supermoun62/Projet_Telerupteur_RF433_V2/Liste_Materiel_Emetteur_Recepteur_Telerupteur_RF433_V2/Liste_Materiel_Emetteur_Telerupteur_RF433_V2.pdf

Liste_Materiel_Emetteur_Telerupteur_RF433_V2

Page 1 sur 1 | https://electroniquepassion.fr/
Reference | Value | TME Electronic | SeedStudio | GoTronic | Lextronic | Conrad
U3 | A000005
J2 | PinHeader_1x02_P2.54mm
D4 | R 2v | SLR-56VR3F (https://www.tme.eu/fr/katalog/?art=SLR-56VR3F)
R2, R4 | 10k - 1 % | MRS25000C1002FCT00 (https://www.tme.eu/fr/katalog/?art=MRS25000C1002FCT00)
J4 | PinHeader_1x03_P2.54mm
U4 | Emetteur | | 113990010 | 05294 (https://www.gotronic.fr/art-kit-emetteur-recepteur-433mhz-18881.htm)
U2 | 24LC256-I_P
R6, R7 | 4k7 - 1 % | MBB02070C4701FCT00 (https://www.tme.eu/fr/katalog/?art=MBB02070C4701FCT00)
J3 | PinHeader_1x01_P2.54mm
D3 | R 2v | SLR-56VR3F (https://www.tme.eu/fr/katalog/?art=SLR-56VR3F)
R8 | 1K5 - 1 % | MRS25000C1501FCT00 (https://www.tme.eu/fr/details/mrs25000c1501fct00/resistances-metallisees-tht-0-6w/vishay/)
D5 | R 2v | SLR-56VR3F (https://www.tme.eu/fr/katalog/?art=SLR-56VR3F)
F1 | 100mA
Support Fusible | | | | | | 530127 (https://www.conrad.fr/p/porte-fusible-eska-506000-506000-adapte-pour-fusible-5-x-20-mm-63-a-250-vac-1-pcs-530127)
D2 | V 2v | OSNG5134A (https://www.tme.eu/fr/details/osng5134a/diodes-led-tht-5mm/optosupply/)
R1, R3, R5 | 3K9 - 1 % | MBB02070C3901FC100 (https://www.tme.eu/fr/details/mbb02070c3901fc100/resistances-metallisees-tht-0-6w/vishay/)
U1 | L7809 | NTE1910 (https://www.tme.eu/fr/details/nte1910/stabilisateurs-de-tension-non-regles/nte-electronics/)
Refroidisseur | | FK210SACB (https://www.tme.eu/fr/details/fk210sacb/radiateurs/fischer-elektronik/)
| Pâte thermique KP12 4.2 g 10 W/mK | | | | | 189069 (https://www.conrad.fr/p/pate-thermique-kerafol-kp12-42-g-10-wmk-temperature-max-150-c-42-g-189069)
C3 | 100nf | CCK-100N (https://www.tme.eu/fr/details/cck-100n/condensateurs-ceramiques-tht-100v/sr-passives/)
C2 | 330nf | BFC233820334 (https://www.tme.eu/fr/details/bfc233820334/condensateurs-polypropylene-x2-y2/vishay/)
C1 | 2200uf | KM2200/25 (https://www.tme.eu/fr/details/km2200_25/condensateurs-electrolytiques-tht-105degc/samxon/km-2200u-25v/)
TR1 | BVEI3022938 220v -12v -1,2VA | BVEI3022938 (https://www.tme.eu/fr/katalog/?search=BVEI3032012&s_field=1000011&s_order=desc)
D1 | B40C1500G | B40C1500G-E4/51 (https://www.tme.eu/fr/details/b40c1500g-e4_51/redresseurs-monophases-a-diodes-ronds/vishay/)
J1 | Conn_01x03 | MKDS 1,5/ 3-5,08 1715734 | | | | 743464 (https://www.conrad.fr/p/bornier-a-vis-phoenix-contact-mkds-15-3-508-1715734-150-mm-nombre-de-poles-3-vert-1-pcs-743464)

Support 8b

Fil pour Arduino | 25932 (https://www.gotronic.fr/art-pack-de-cables-de-connexion-12411.htm)
Strap | | 15-AT (https://www.lextronic.fr/cavalier-pas-2-54-mm-3613.html)
Con Header mâle | 48004 (https://www.gotronic.fr/art-connecteur-ard010-18114.htm) | CC076 (https://www.lextronic.fr/module/ambjolisearch/jolisearch?s=cc076)
