supermoun62/Projet_Telerupteur_RF433_V2/Liste_Materiel_Emetteur_Recepteur_Telerupteur_RF433_V2/Liste_Materiel_Recepteur_Telerupteur_RF433_V2.pdf

Liste_Materiel_Recepteur_Telerupteur_RF433_V2

Page 1 sur 1 | https://electroniquepassion.fr/
Reference | Value | TME Electronic | SeedStudio | GoTronic | Lextronic | Farnell
C1 | 2200uf | KM2200/25 (https://www.tme.eu/fr/details/km2200_25/condensateurs-electrolytiques-tht-105degc/samxon/km-2200u-25v/)
C2, C4 | 330nf | BFC233820334 (https://www.tme.eu/fr/details/bfc233820334/condensateurs-polypropylene-x2-y2/vishay/)
C3, C5 | 100nf | CCK-100N (https://www.tme.eu/fr/details/cck-100n/condensateurs-ceramiques-tht-100v/sr-passives/)
D1 | B40C1500G | SLR-56VR3F (https://www.tme.eu/fr/katalog/?art=SLR-56VR3F)
D2, D3 | V 2v | OSNG5134A (https://www.tme.eu/fr/details/osng5134a/diodes-led-tht-5mm/optosupply/)
D4, D5 | R 2v | SLR-56VR3F (https://www.tme.eu/fr/katalog/?art=SLR-56VR3F)
D6, D7 | Diode | 1N4007 (https://www.tme.eu/fr/katalog/?search=1n4007&s_field=1000011&s_order=desc)
F1 | 250mA
F2, F3 | 3,15A
*3 | Support Fusibles 696108003002 | ZHL77 (https://www.tme.eu/fr/details/zhl77/porte-fusibles-pcb/stelvio-kontek/ptf-77/) | | | | 2471682
*3 | Capot 696122003001 | ZHL7X-H (https://www.tme.eu/fr/details/zhl7x-h/porte-fusibles-pcb/stelvio-kontek/bs232/) | | | | 2471684
J1 | Connecteur 3pins | MKDSN2,5/3-5,08-1888690 (https://www.tme.eu/fr/katalog/?search=MKDSN2%2C5%2F3-5%2C08-1888690&s_field=1000011&s_order=desc)
J2, J4, J5 | Connecteur 2pins | MKDSN2,5/2-5,08-1888687 (https://www.tme.eu/fr/katalog/?search=MKDSN2%2C5%2F2-5%2C08-1888687&s_field=1000011&s_order=desc)
J3 | PinHeader_1x02_P2.54mm | | | 08000 | CC078
J3 | Strap | | | | 15-AT (https://www.lextronic.fr/cavalier-pas-2-54-mm-3613.html)
K1, K2 | Relais | ALQ312 (https://www.tme.eu/fr/katalog/?search=alq312&s_field=1000011&s_order=desc) | | | | 2503678
R1, R2, R3, R4 | 3K9 - 1 % | MBB02070C3901FC100 (https://www.tme.eu/fr/details/mbb02070c3901fc100/resistances-metallisees-tht-0-6w/vishay/)
R5, R6 | 4K7 - 1 % | MBB02070C4701FCT00 (https://www.tme.eu/fr/details/mbb02070c4701fct00/resistances-metallisees-tht-0-6w/vishay/)
R7, R8 | 200 - 1 % | MF0207FTE-255R (https://www.tme.eu/fr/details/mf0207fte-255r/resistances-metallisees-tht-0-6w/yageo/mf0207fte52-255r/)
| Transfo 220v -15v – 2,3VA | BV EI 303 2013 (https://www.tme.eu/fr/details/bvei3032013/transformateurs-pour-pcb/hahn/bv-ei-303-2013/#)
U1 | Régulateur | L7812CV-DG (https://www.tme.eu/fr/katalog/?search=L7812&s_field=1000011&s_order=desc)
*2 | Refroidisseur | FK210SACB (https://www.tme.eu/fr/katalog/?search=FK210SACB&s_field=1000011&s_order=desc)
U2 | Régulateur | NTE1910 (https://www.tme.eu/fr/details/nte1910/stabilisateurs-de-tension-non-regles/nte-electronics/)
| Pâte thermique KP12 4.2 g 10 W/mK
U3 | A000005
U4 | Mémoire | 24LC256-I/PG (https://www.tme.eu/fr/details/24lc256-i_pg/memoires-eeprom-de-serie/microchip-technology/24lc256-i-p/)
U5 | Recepteur | | 113990010 | 05294 (https://www.gotronic.fr/art-kit-emetteur-recepteur-433mhz-18881.htm)
U6, U7 | Optocoupleur | 4N35 (https://www.tme.eu/fr/katalog/?search=4N35&s_field=1000011&s_order=desc)
*2 | Support 6b | ICVT-6P (https://www.tme.eu/fr/details/icvt-6p/supports-dip-standard/connfly/ds1009-06at1nx/) | | | | 179993
