supermoun62/Projet_Telerupteur_RF433_V2/Doc_Tech_Emetteur_Recepteur_Telerupteur_RF433_V2/fiche-technique-PinHeader-254.pdf

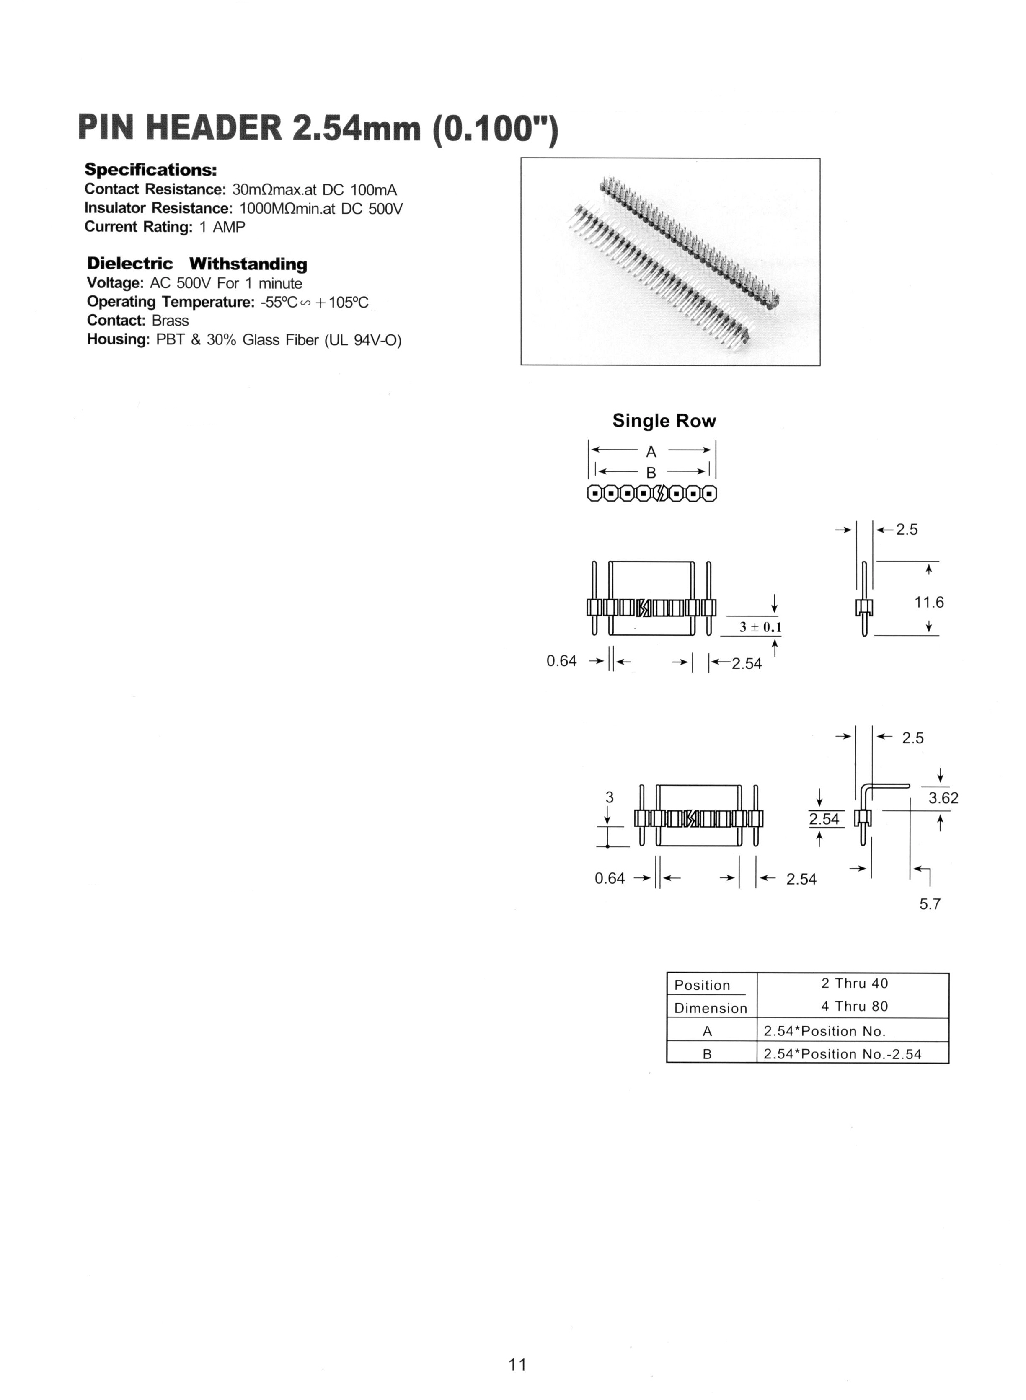
[picture p13: page 1]
