supermoun62/Projet_Telerupteur_RF433_V2/PCB_PDF_Telerupteur_Emetteur_V2/Telerupteur_Emetteur_RF433_V2-B_Mask.pdf

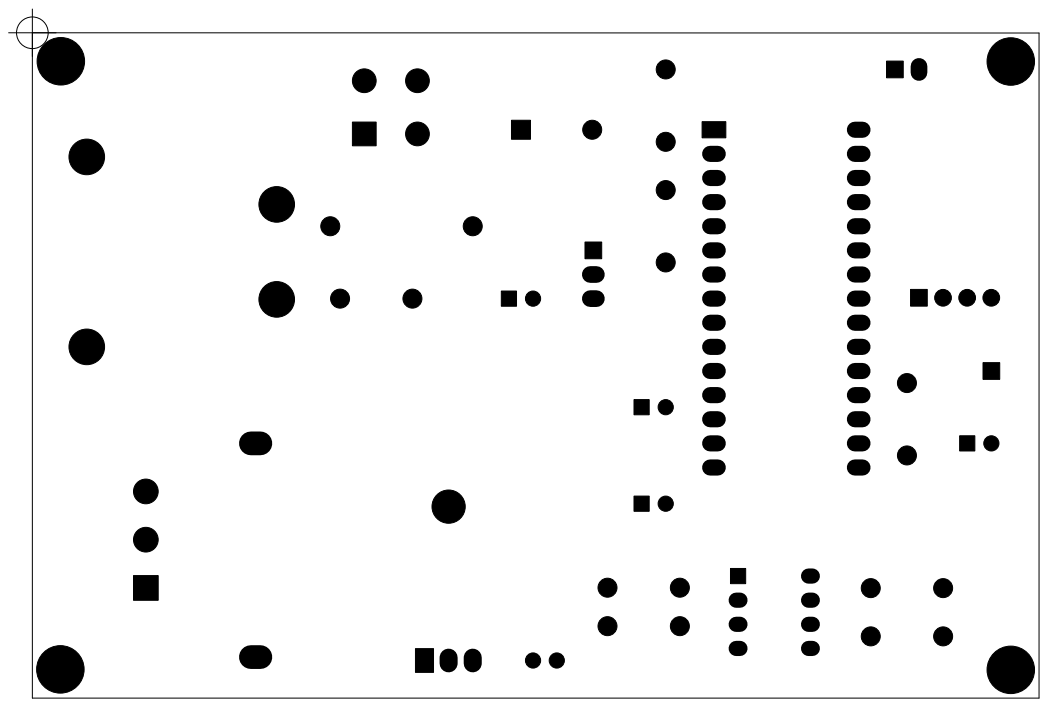
[picture p17: page 1]
