supermoun62/Projet_Telerupteur_RF433_V2/PCB_PDF_Telerupteur_Emetteur_V2/Telerupteur_Emetteur_RF433_V2-Dwgs_User.pdf

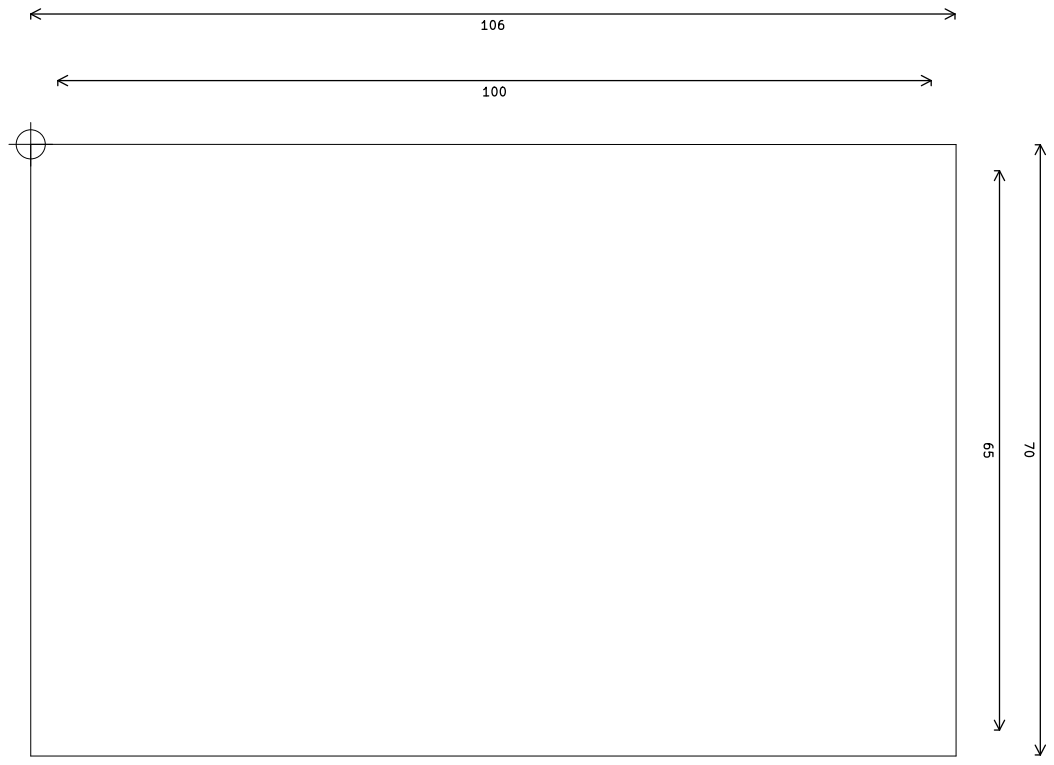
[picture p19: page 1]
