supermoun62/Projet_Telerupteur_RF433_V2/PCB_PDF_Telerupteur_Emetteur_V2/Telerupteur_Emetteur_RF433_V2-F_CrtYd.pdf

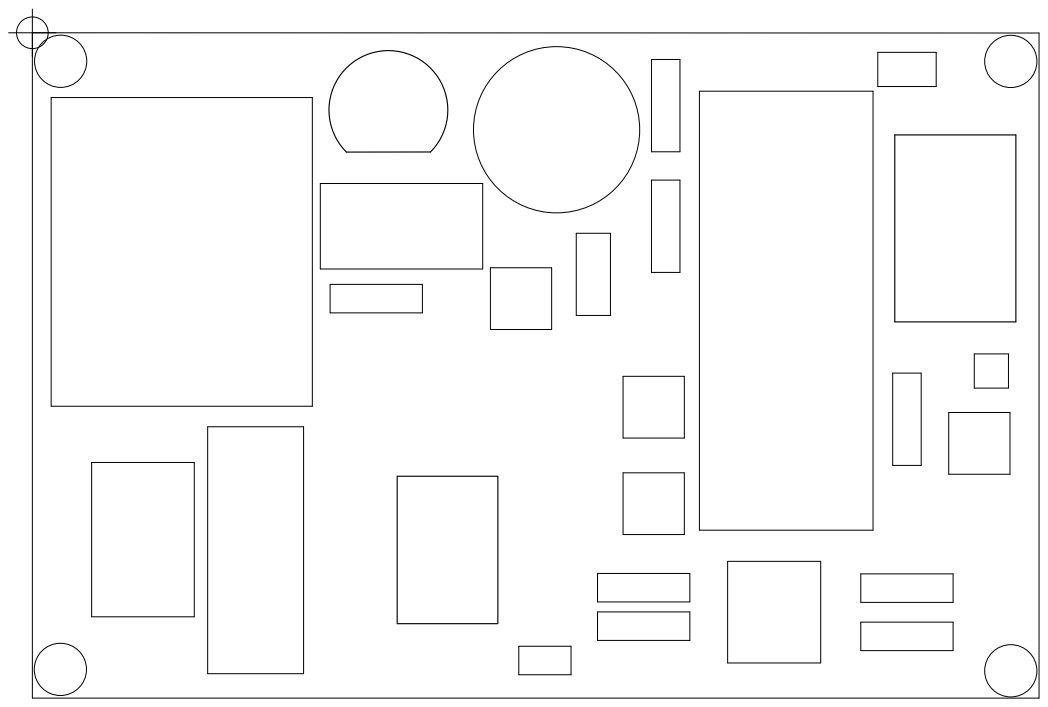
[picture p20: page 1]
