supermoun62/Projet_Telerupteur_RF433_V2/PCB_PDF_Telerupteur_Recepteur_V2/Telerupteur_Recepteur_RF433_V2-B_Cu.pdf

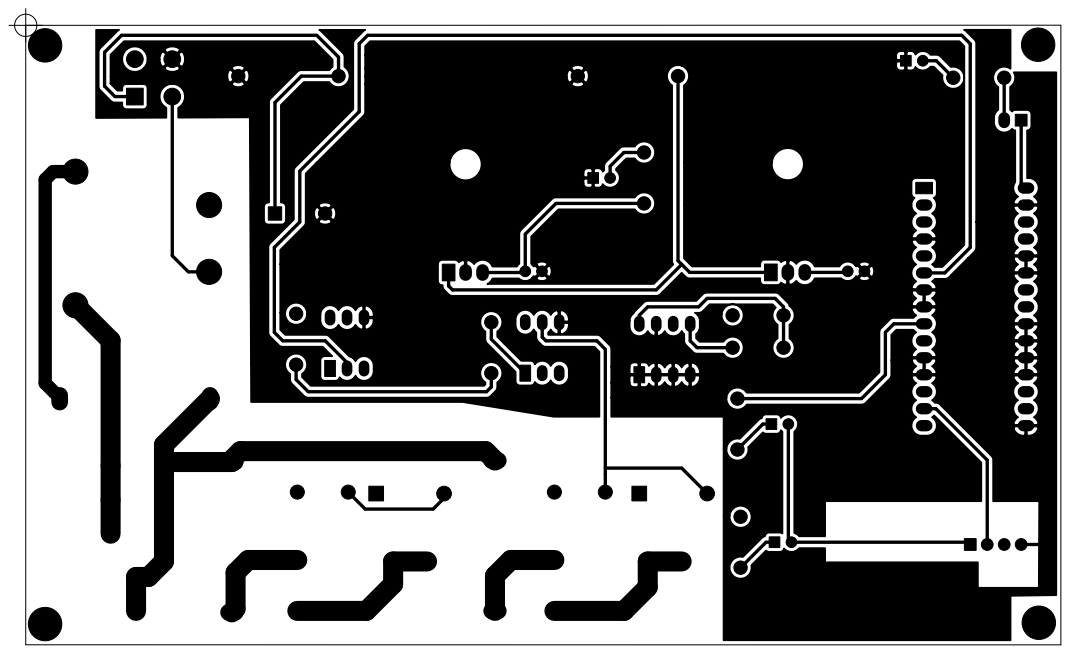
[picture p24: page 1]
