supermoun62/Projet_Telerupteur_RF433_V2/PCB_PDF_Telerupteur_Recepteur_V2/Telerupteur_Recepteur_RF433_V2-Cmts_User.pdf

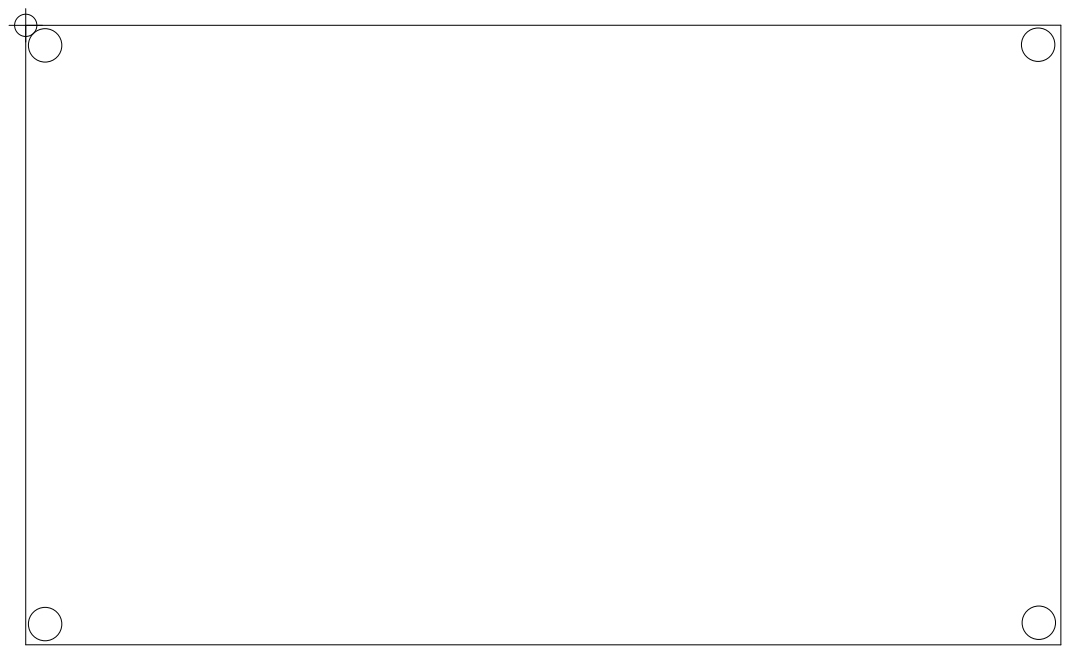
[picture p26: page 1]
