supermoun62/Projet_Telerupteur_RF433_V2/PCB_PDF_Telerupteur_Recepteur_V2/Telerupteur_Recepteur_RF433_V2-Dwgs_User.pdf

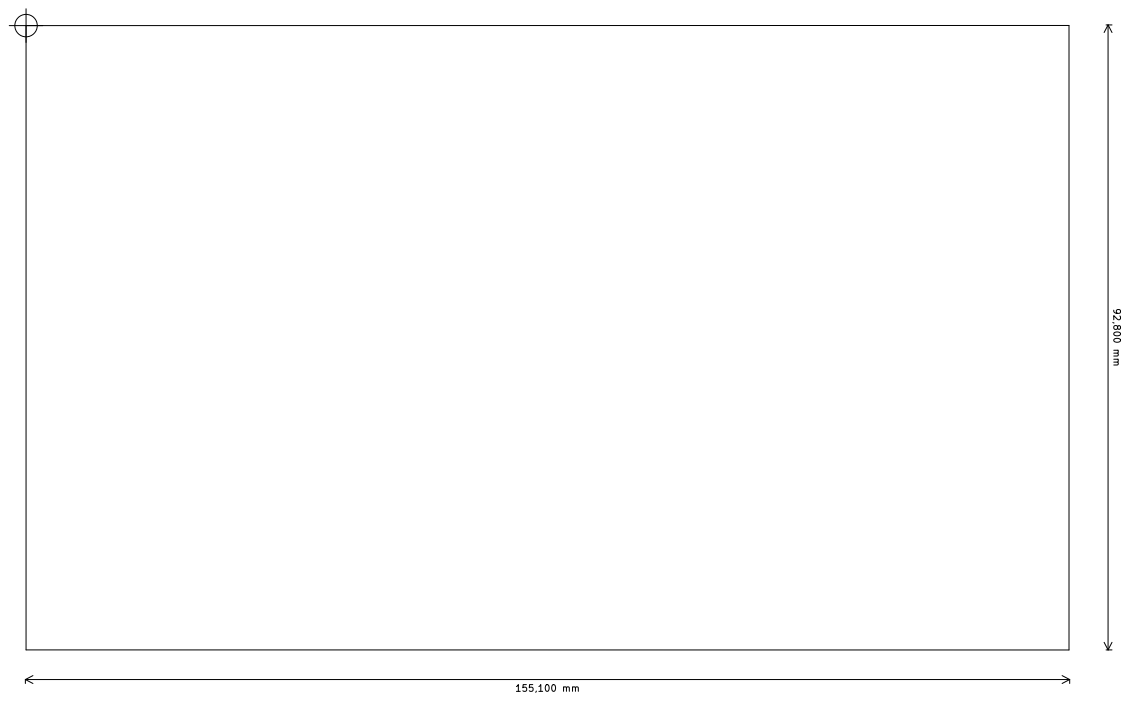
[picture p27: page 1]
