supermoun62/Projet_Telerupteur_RF433_V2/PCB_PDF_Telerupteur_Recepteur_V2/Telerupteur_Recepteur_RF433_V2-F_CrtYd.pdf

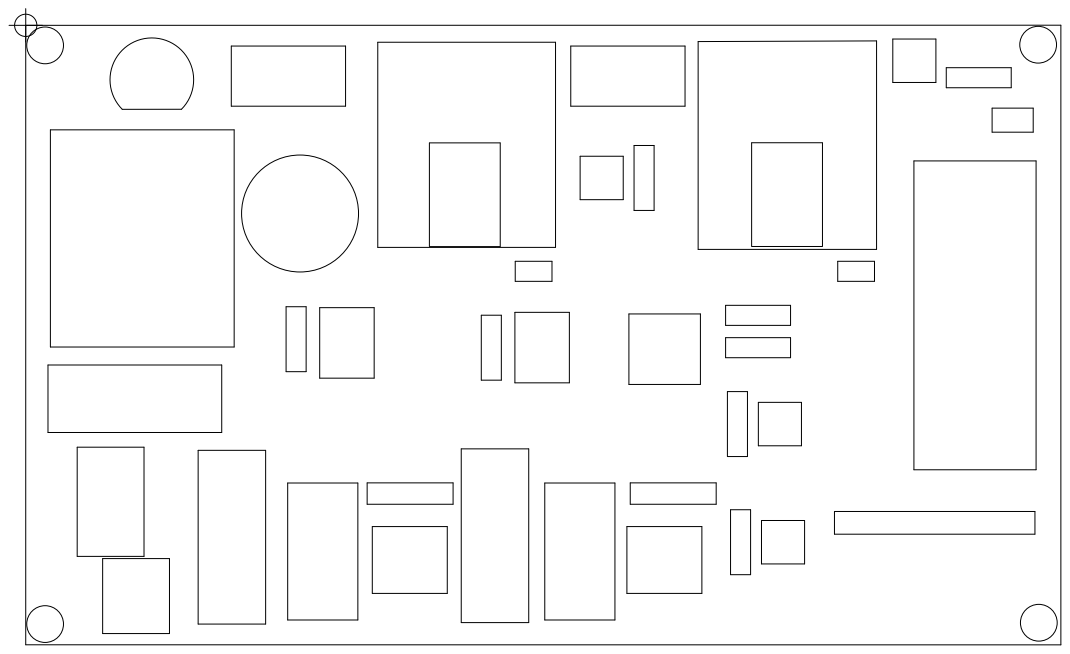
[picture p28: page 1]
