supermoun62/Projet_Telerupteur_RF433_V2/Schemas_Emetteur_Recepteur_Telerupteur_RF433_V2/Schema_Telerupteur_Emetteur_RF433_V2.pdf

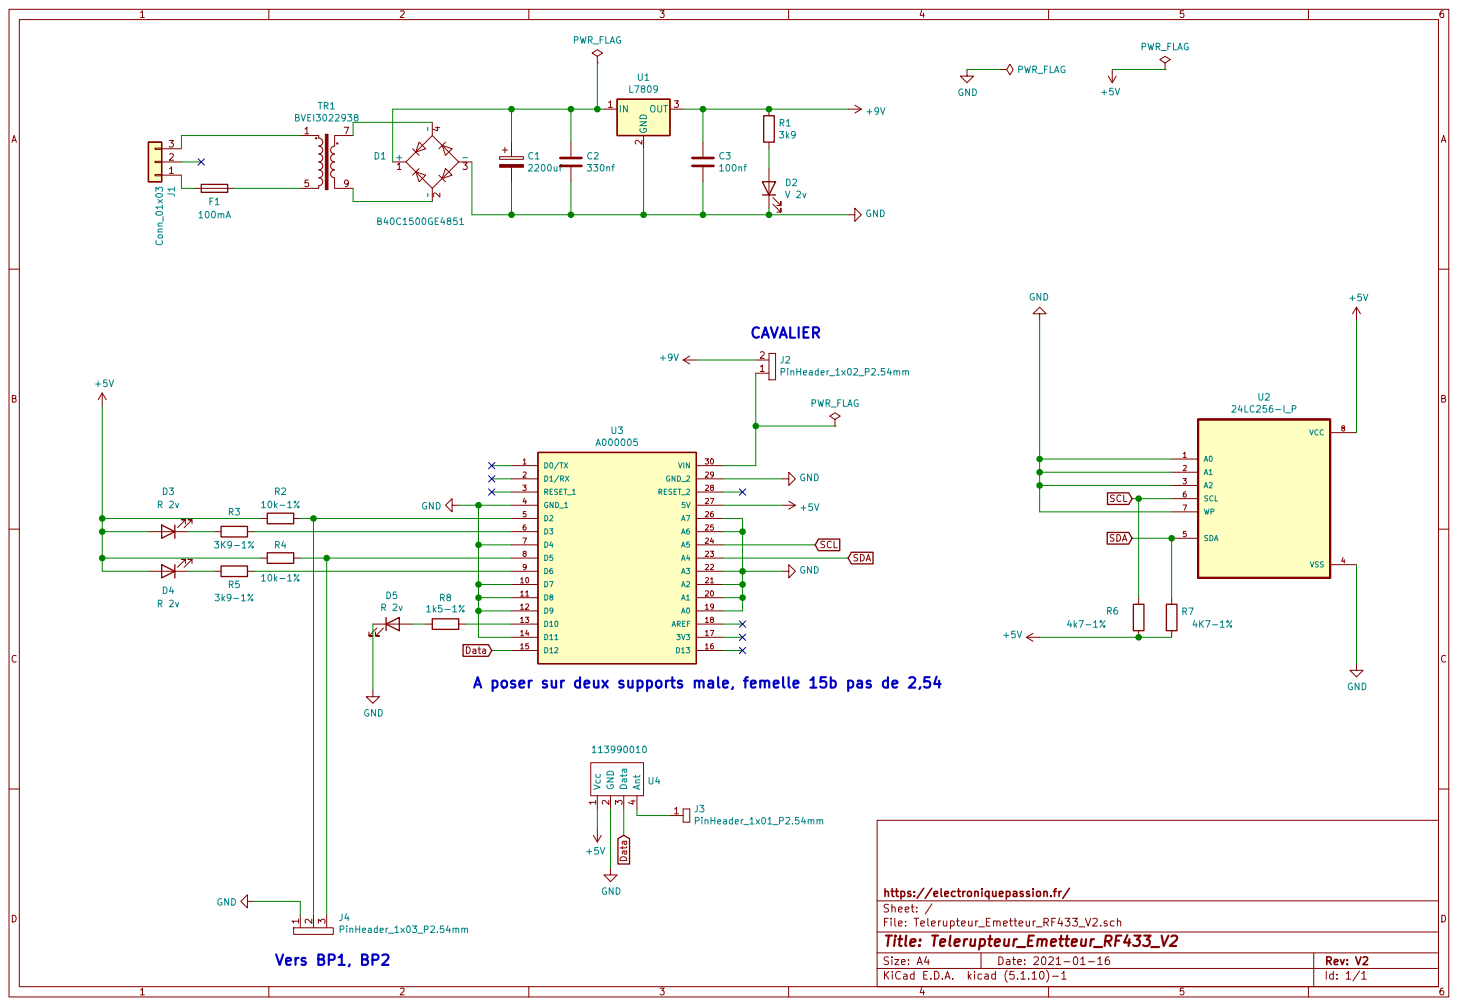
[picture p32: page 1]

A poser sur deux supports male, femelle 15b pas de 2,54
