supermoun62/Projet_Telerupteur_RF433_V2/Schemas_Emetteur_Recepteur_Telerupteur_RF433_V2/Schema_Telerupteur_Recepteur_RF433_V2.pdf

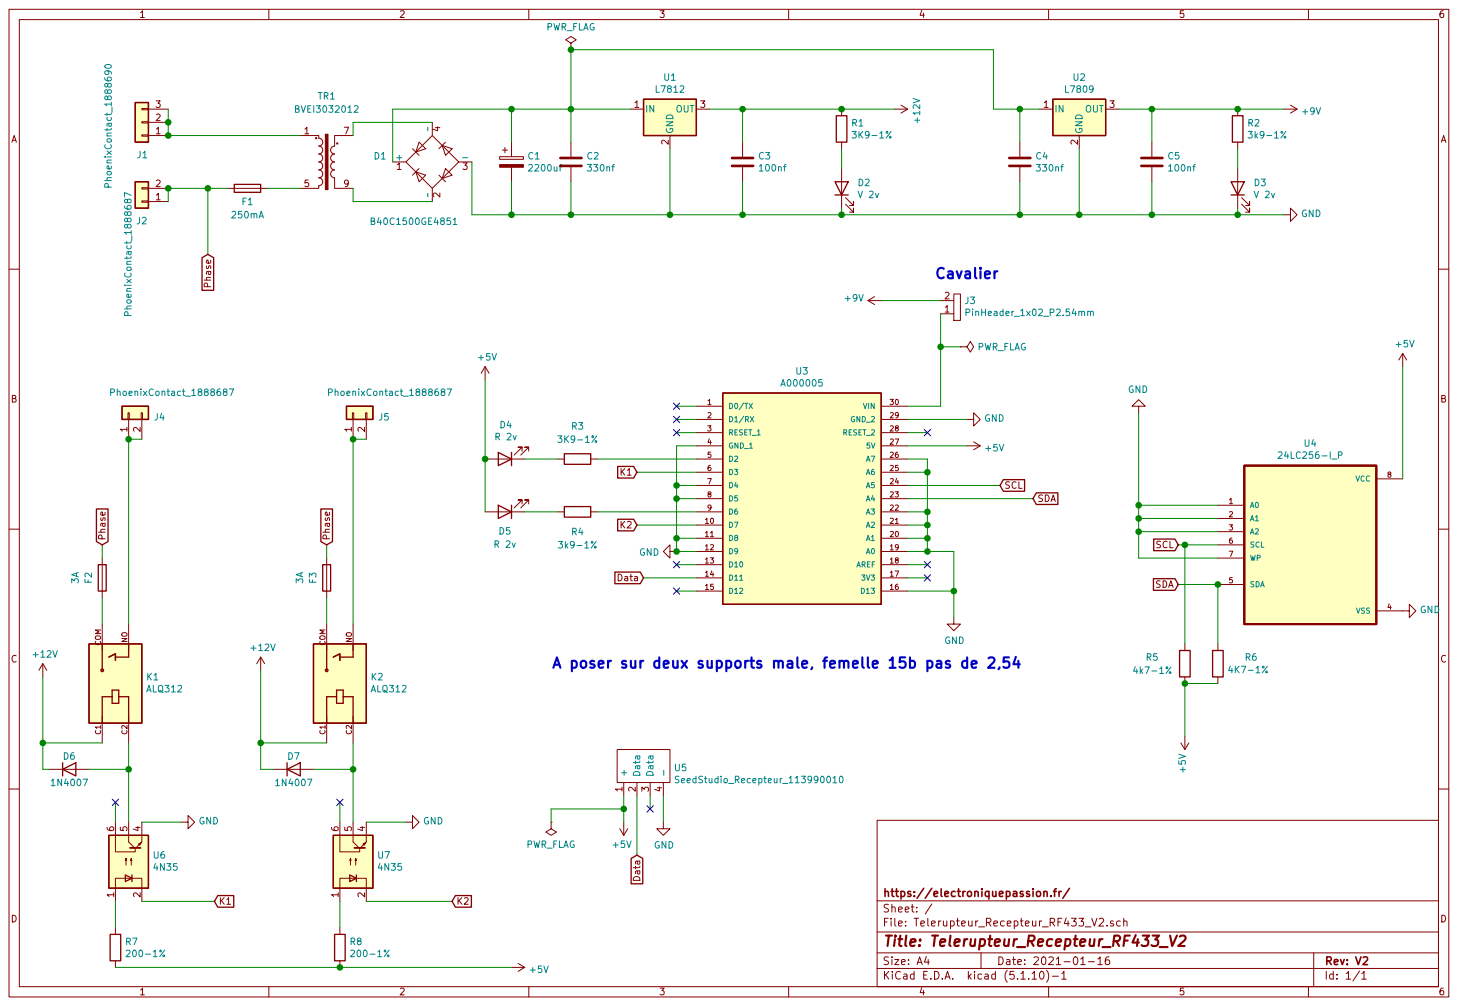
[picture p33: page 1]

File: Telerupteur_Recepteur_RF433_V2.sch Sheet: / https://electroniquepassion.fr/
