supermoun62/Projet_Telerupteur_RF433_V2/simpleBouton/examples/exemple_12_bouton_action_repetition/exemple_12_bouton_action_repetition.ino

#include "simpleBouton.h"

const uint8_t pin_bouton = 3;//cablage pin---BP---GND

boutonAction bouton(pin_bouton);

void clic() {Serial.println("clic");}

void setup()
{
  Serial.begin(115200);
  bouton.attacher(clic);
  bouton.activerRepetition(); //maintenir le bouton enfonce pour voir le resultat
}

void loop()
{
  bouton.actualiser();
}
