supermoun62/Projet_Telerupteur_RF433_V2/simpleBouton/examples/exemple_13_bouton_action_double_clic/exemple_13_bouton_action_double_clic.ino

#include "simpleBouton.h"

const uint8_t pin_bouton = 3;//cablage pin---BP---GND

boutonAction bouton(pin_bouton);

void simpleClic() {Serial.println("simple clic");}
void doubleClic() {Serial.println("double clic");}

void setup()
{
  Serial.begin(115200);
  bouton.attacher(simpleClic, doubleClic);
}

void loop()
{
  bouton.actualiser();
}
